sFer8/freETarget-3D-Printed-Housing/Images/Image 1.png

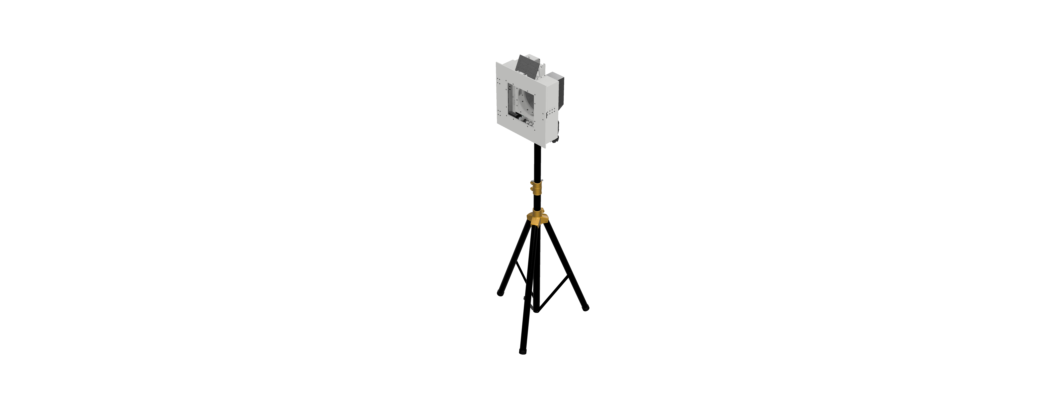
Images/Image 1.png
