sFer8/freETarget-3D-Printed-Housing/Images/Image 2.png

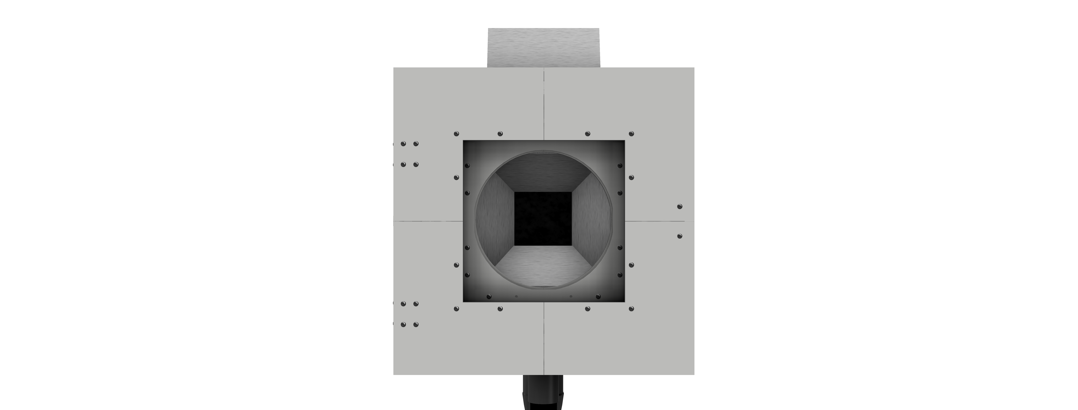
Images/Image 2.png
