sFer8/freETarget-3D-Printed-Housing/Images/Image 5.png

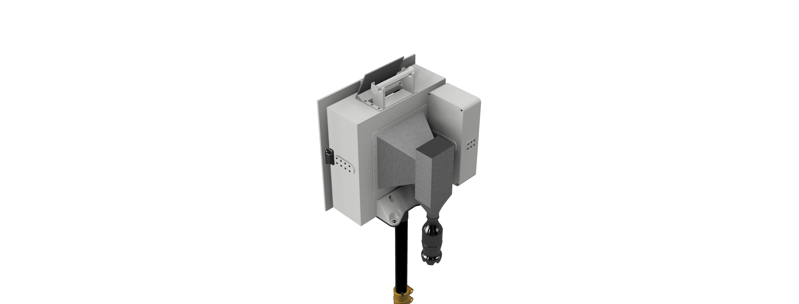
Images/Image 5.png
