sFer8/freETarget-3D-Printed-Housing/Images/Images of Physical Target/IMG_8709.jpg

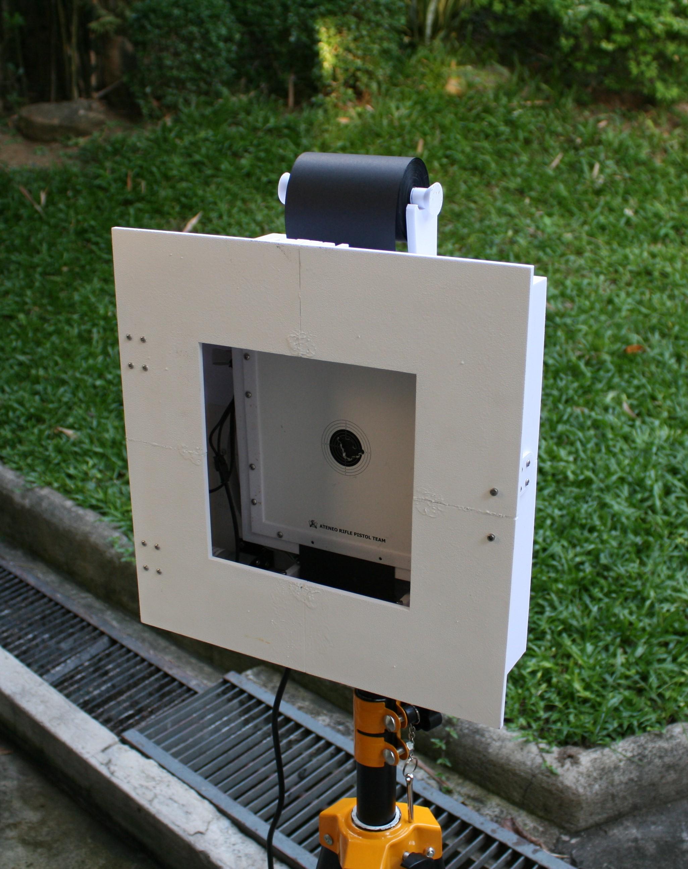
Images/Images of Physical Target/IMG_8709.jpg
