sFer8/freETarget-3D-Printed-Housing/Images/Images of Physical Target/IMG_8710.jpg

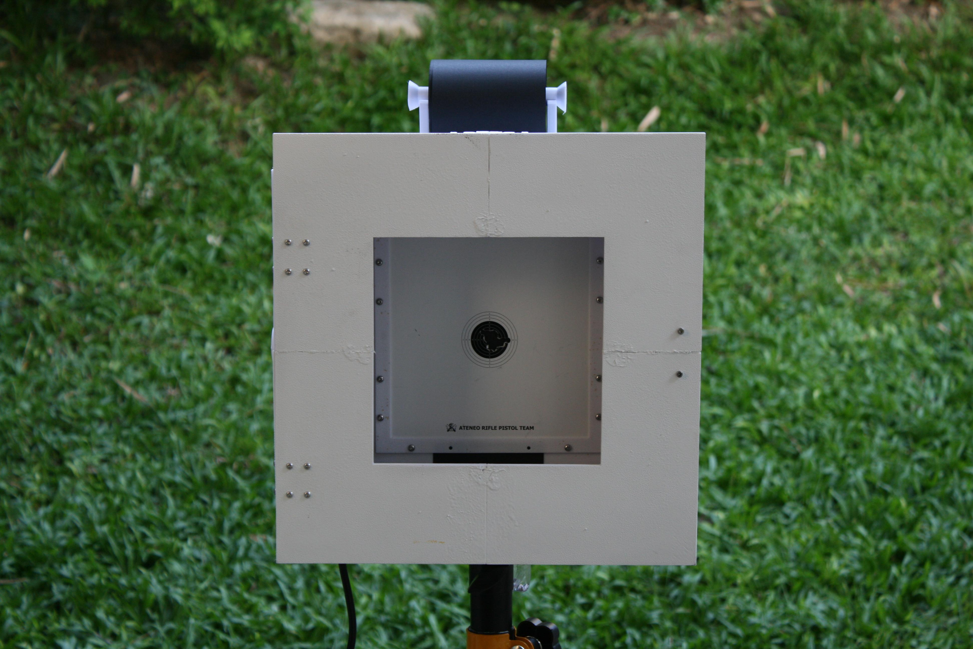
Images/Images of Physical Target/IMG_8710.jpg
