sFer8/freETarget-3D-Printed-Housing/OBJ/Target Holder/Default (17x17cm target)/(3mm Steel )Metal Plate.obj

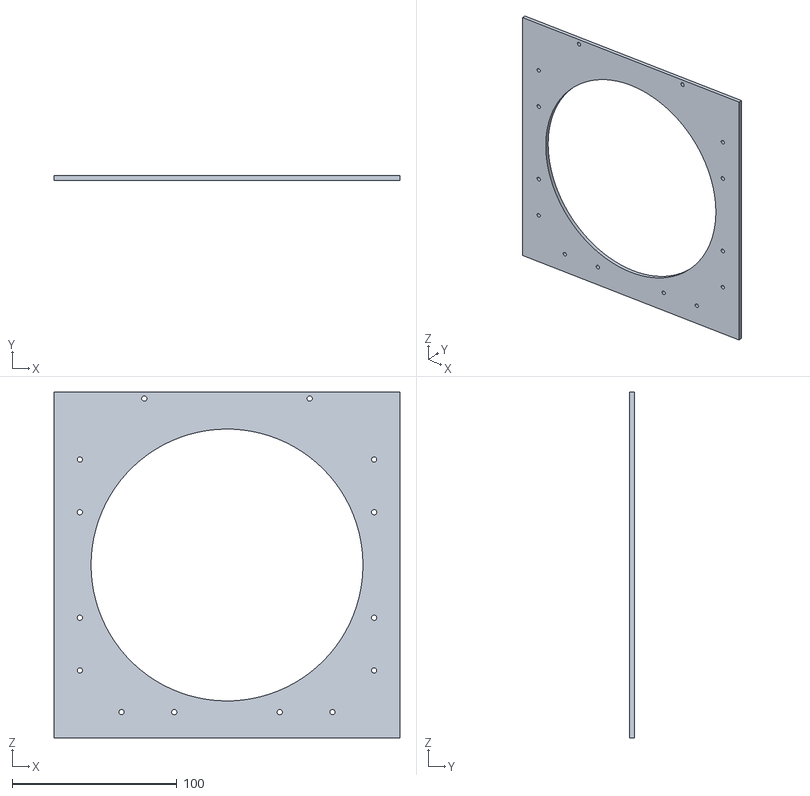
[picture p37: CAD file, 2025-11-06]
OBJ/Target Holder/Default (17x17cm target)/(3mm Steel )Metal Plate.obj
210.0 x 3.00 x 210.0
