sFer8/freETarget-3D-Printed-Housing/OBJ/Target Holder/Witness paper Guide.obj

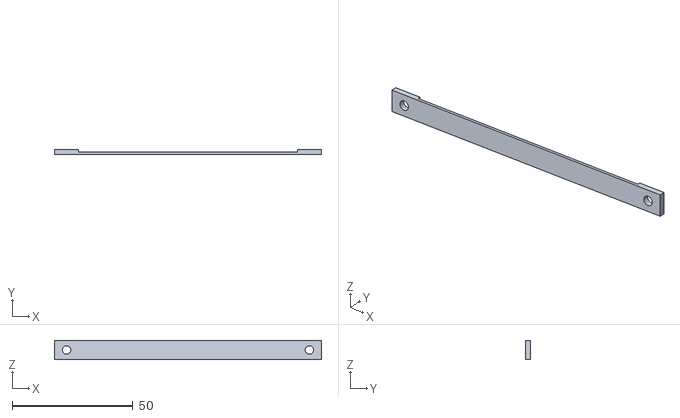
[picture p38: CAD file, 2025-11-06]
OBJ/Target Holder/Witness paper Guide.obj
110.4 x 2.00 x 8.00
