sFer8/freETarget-3D-Printed-Housing/OBJ/Witness Paper Holder/Witness Paper Holder.obj

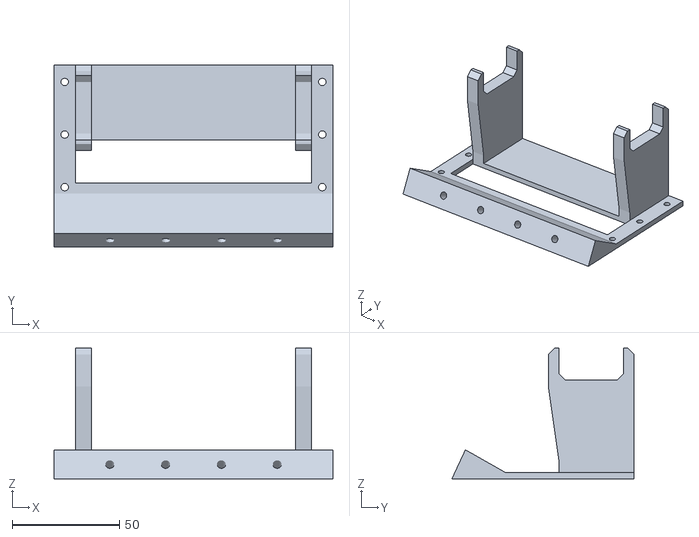
[picture p39: CAD file, 2025-11-06]
OBJ/Witness Paper Holder/Witness Paper Holder.obj
130.0 x 85.0 x 61.0
