sFer8/freETarget-3D-Printed-Housing/DWG/Housing Plate.dxf

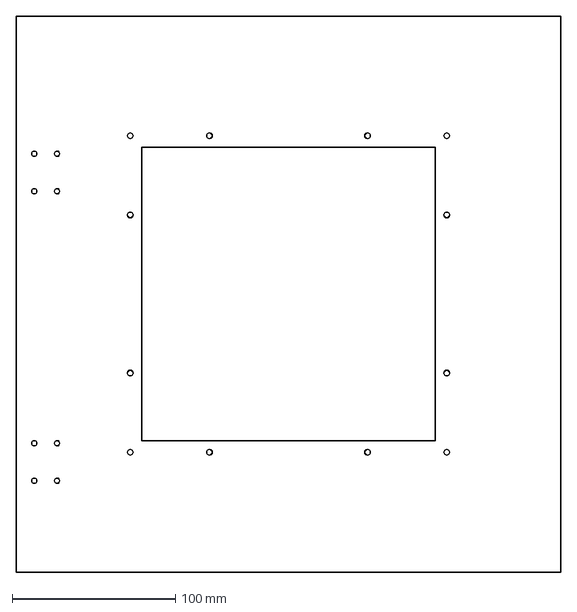
[picture p40: CAD file, 2025-06-11]
DWG/Housing Plate.dxf
334.0 x 341.0 mm
