sFer8/freETarget-3D-Printed-Housing/DXF/SUIS Style Pellet trap/Right.dxf

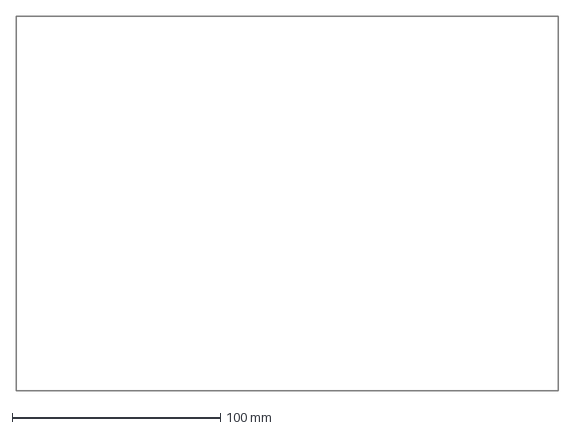
[picture p41: CAD file, 2025-11-06]
DXF/SUIS Style Pellet trap/Right.dxf
260.3 x 180.0 mm
