sFer8/freETarget-3D-Printed-Housing/DXF/SUIS Target Holder Metal Plate.dxf

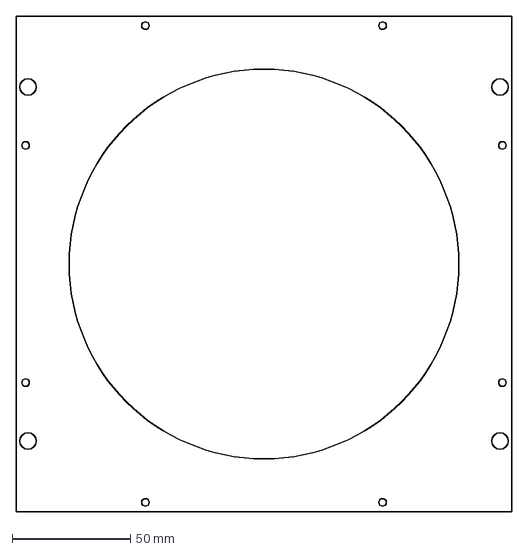
[picture p42: CAD file, 2025-11-06]
DXF/SUIS Target Holder Metal Plate.dxf
210.0 x 210.0 mm
