sFer8/freETarget-3D-Printed-Housing/OBJ/(Steel plates) SUIS Style Pellet trap/(2mm Steel) Bottom.obj

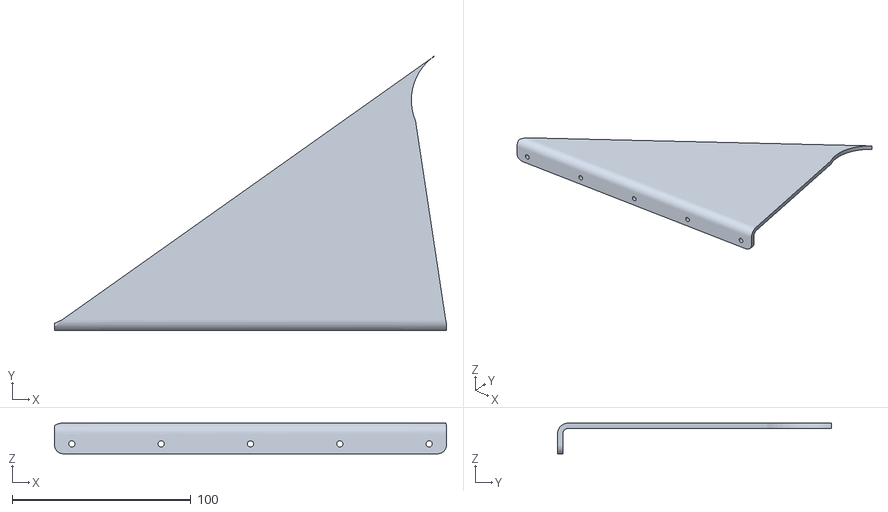
[picture p43: CAD file, 2025-11-06]
OBJ/(Steel plates) SUIS Style Pellet trap/(2mm Steel) Bottom.obj
219.4 x 153.4 x 17.2
