sFer8/freETarget-3D-Printed-Housing/OBJ/Electronics Box/Box/Electronics Box Top.obj

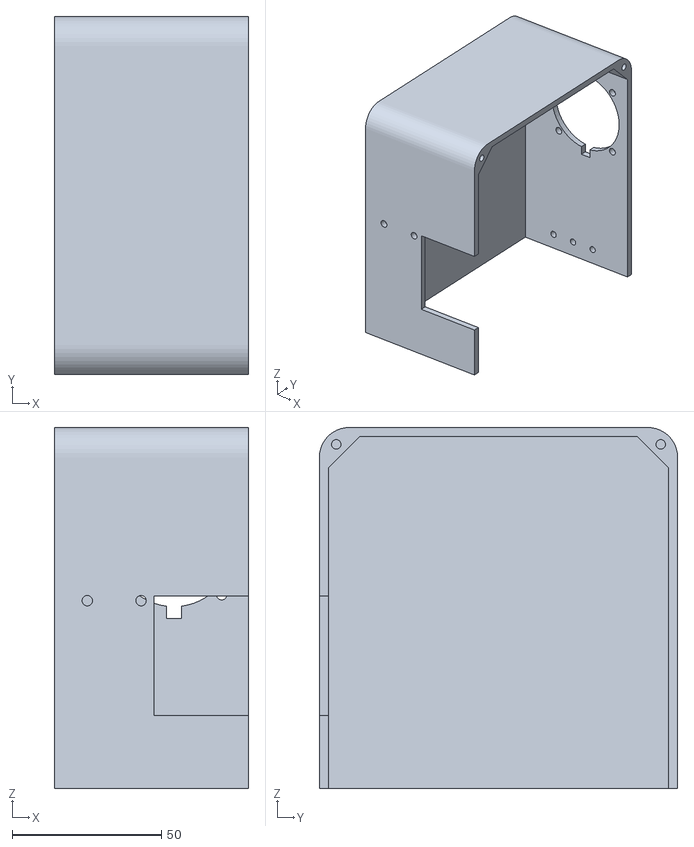
[picture p44: CAD file, 2025-11-06]
OBJ/Electronics Box/Box/Electronics Box Top.obj
65.0 x 120.0 x 120.9
