sFer8/freETarget-3D-Printed-Housing/OBJ/Housing/Face/Top Right.obj

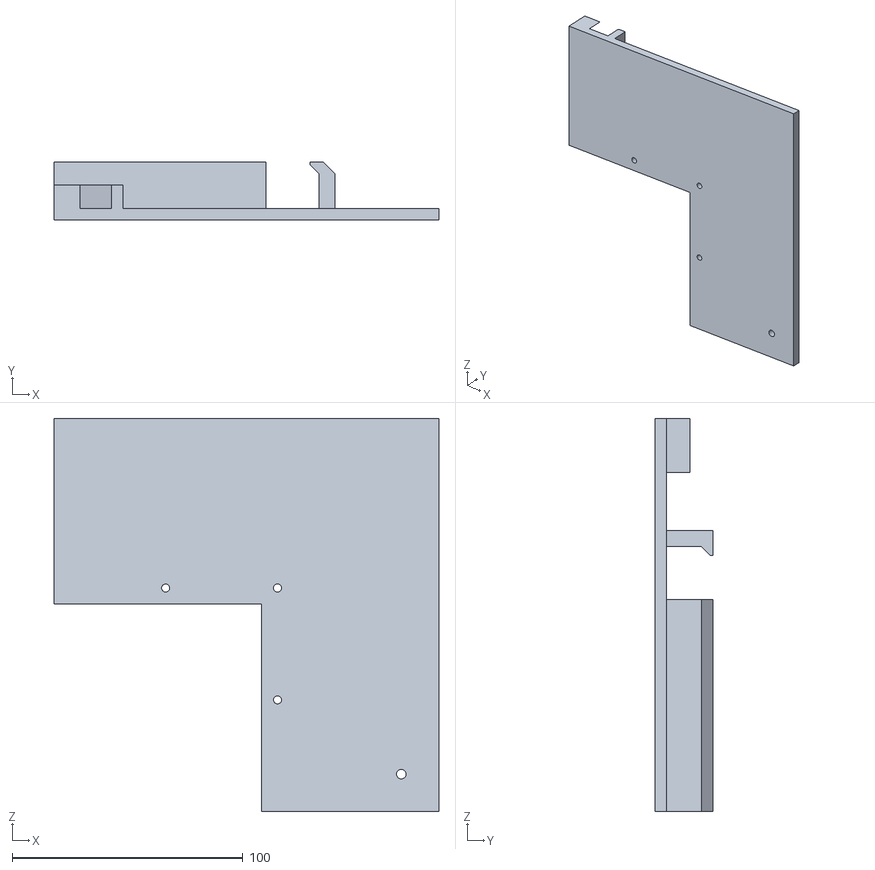
[picture p45: CAD file, 2025-11-06]
OBJ/Housing/Face/Top Right.obj
166.9 x 25.0 x 170.4
