sFer8/freETarget-3D-Printed-Housing/OBJ/Joining Plates/Dovetail wedge Left.obj

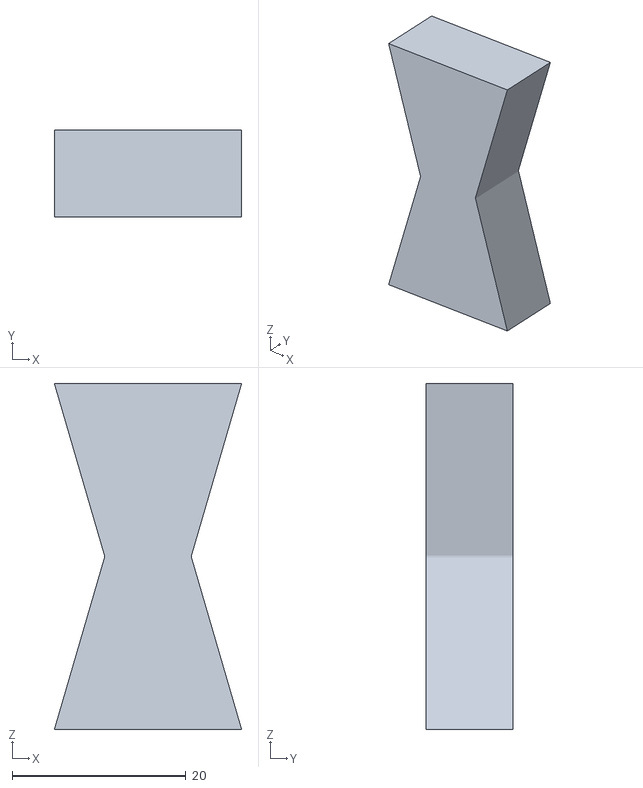
[picture p46: CAD file, 2025-11-06]
OBJ/Joining Plates/Dovetail wedge Left.obj
21.6 x 10.0 x 39.8
