sFer8/freETarget-3D-Printed-Housing/OBJ/Merged/Face Plate.obj

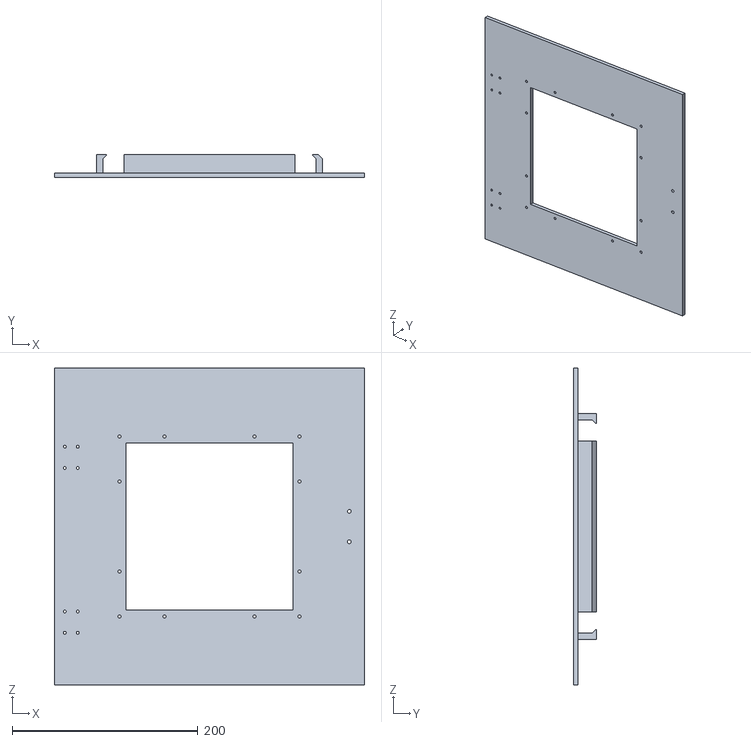
[picture p47: CAD file, 2025-01-14]
OBJ/Merged/Face Plate.obj
334.0 x 25.0 x 341.0
