sFer8/freETarget-3D-Printed-Housing/OBJ/Target Holder/7 Inch wide target/Metal Plate for 7in Target.dxf

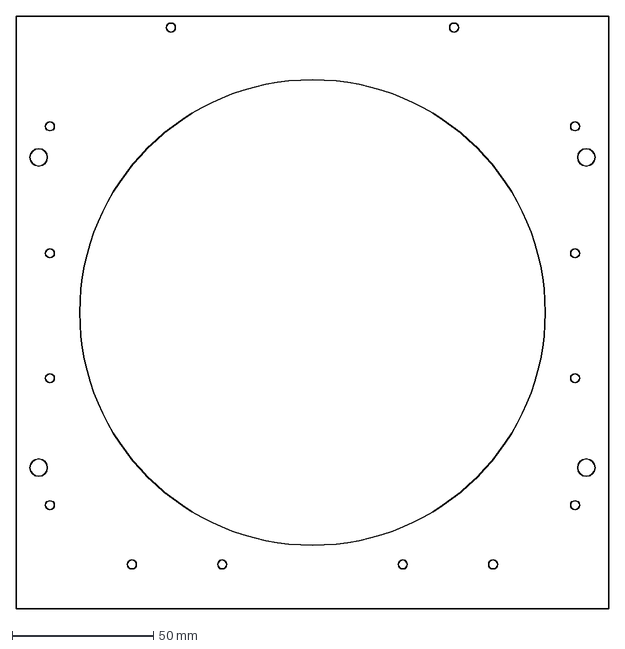
[picture p48: CAD file, 2025-11-23]
OBJ/Target Holder/7 Inch wide target/Metal Plate for 7in Target.dxf
210.0 x 210.0 mm
