sFer8/freETarget-3D-Printed-Housing/OBJ/Target Holder/Default/Targe Holder.obj

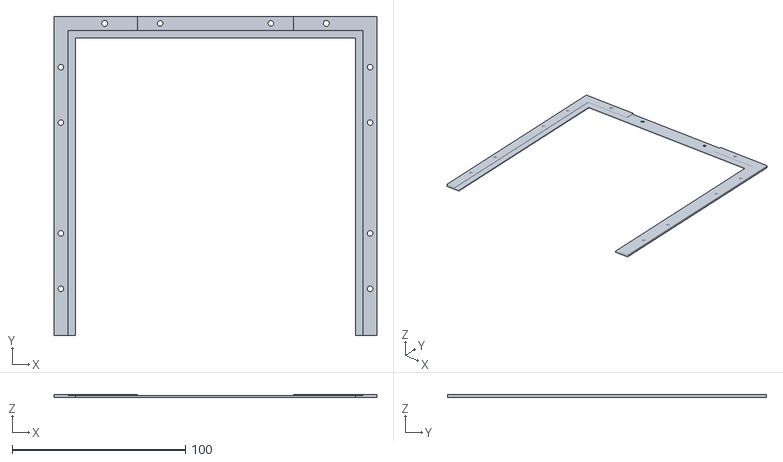
[picture p49: CAD file, 2025-01-06]
OBJ/Target Holder/Default/Targe Holder.obj
186.6 x 184.3 x 2.00
