sFer8/freETarget-3D-Printed-Housing/OBJ/Target Holder/SUIS Target/SUIS Knob 1.obj

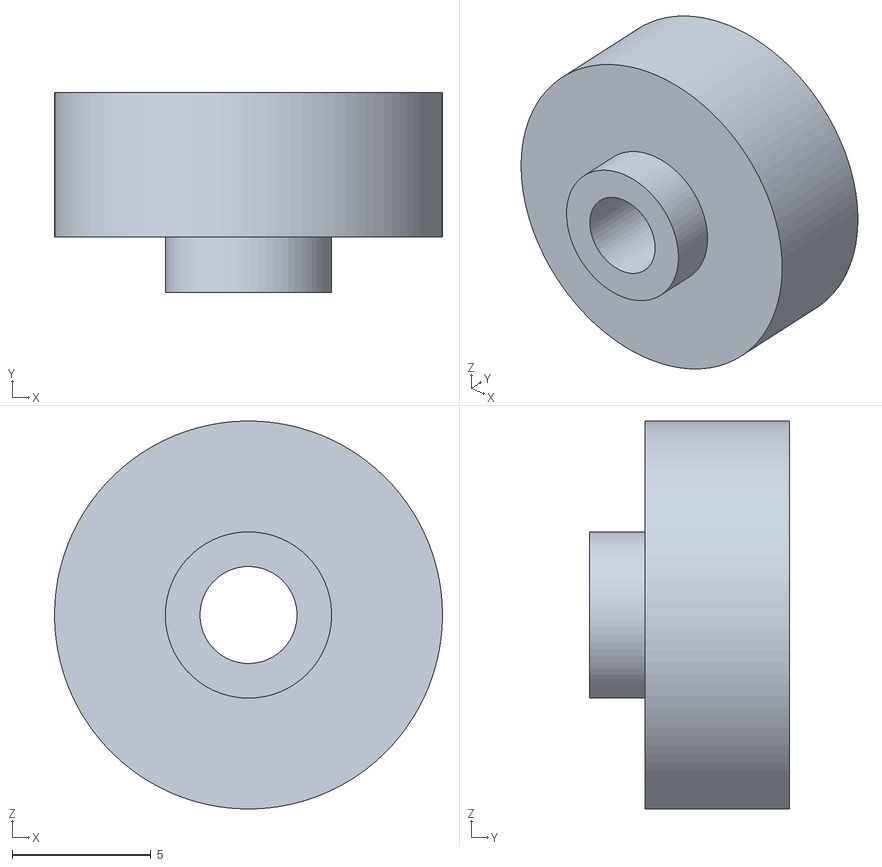
[picture p50: CAD file, 2025-11-06]
OBJ/Target Holder/SUIS Target/SUIS Knob 1.obj
14.0 x 7.20 x 14.0
