sFer8/freETarget-3D-Printed-Housing/OBJ/Witness Paper Holder/(3mm Steel) Steel Pellet Deflector.obj

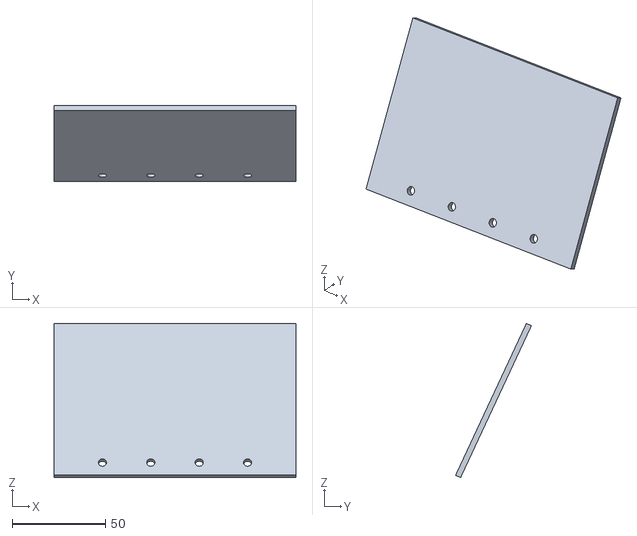
[picture p51: CAD file, 2025-11-06]
OBJ/Witness Paper Holder/(3mm Steel) Steel Pellet Deflector.obj
130.0 x 40.8 x 82.8
