sFer8/freETarget-3D-Printed-Housing/DWG/SIUS metal plate.dxf

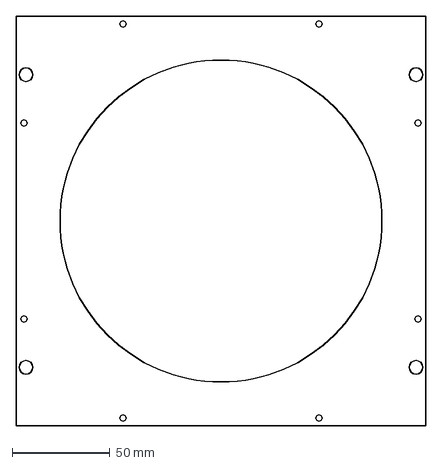
[picture p52: CAD file, 2025-06-11]
DWG/SIUS metal plate.dxf
210.0 x 210.0 mm
