sFer8/freETarget-3D-Printed-Housing/DXF/Housing Metal Plate.dxf

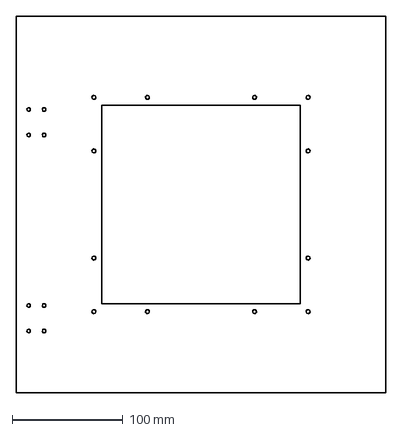
[picture p53: CAD file, 2025-11-06]
DXF/Housing Metal Plate.dxf
334.0 x 341.0 mm
