sFer8/freETarget-3D-Printed-Housing/DXF/SUIS Style Pellet trap/Left.dxf

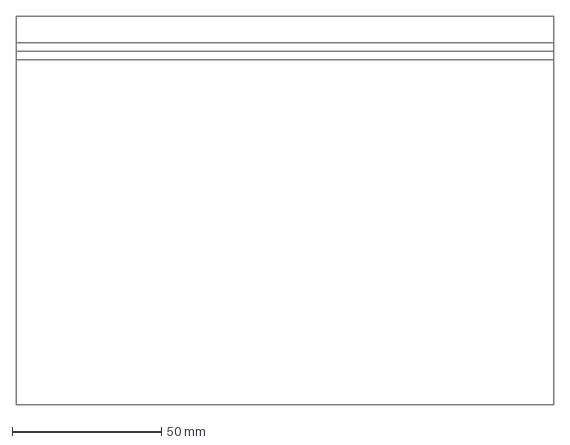
[picture p54: CAD file, 2025-11-06]
DXF/SUIS Style Pellet trap/Left.dxf
180.0 x 130.1 mm
