sFer8/freETarget-3D-Printed-Housing/OBJ/(Steel plates) SUIS Style Pellet trap/(2mm Steel) Left.obj

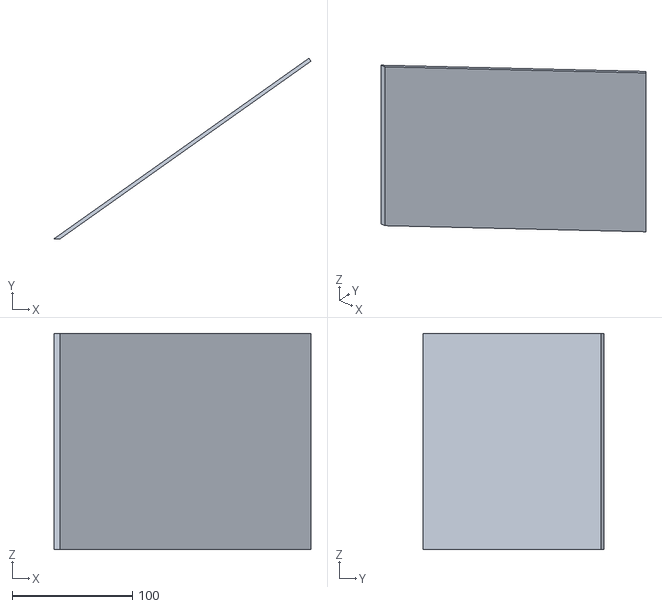
[picture p55: CAD file, 2025-11-06]
OBJ/(Steel plates) SUIS Style Pellet trap/(2mm Steel) Left.obj
214.1 x 150.4 x 180.0
