sFer8/freETarget-3D-Printed-Housing/OBJ/Joining Plates/Electronics Cover Joining Plate.obj

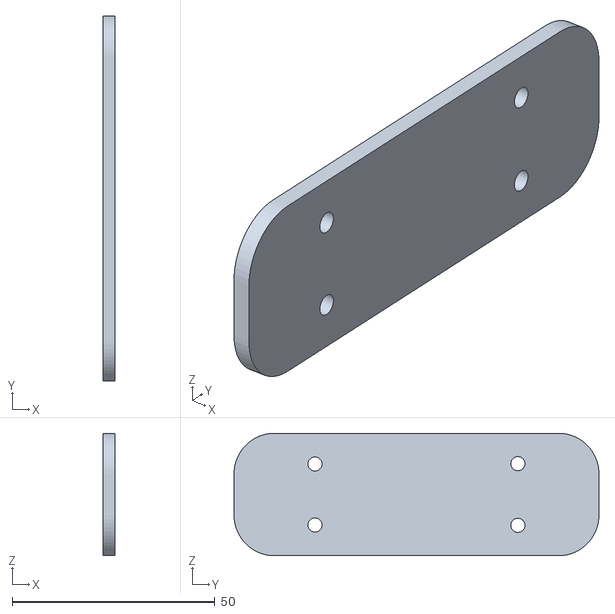
[picture p57: CAD file, 2025-11-06]
OBJ/Joining Plates/Electronics Cover Joining Plate.obj
3.00 x 90.0 x 30.2
