sFer8/freETarget-3D-Printed-Housing/OBJ/Merged/Electronics Box Bottom.obj

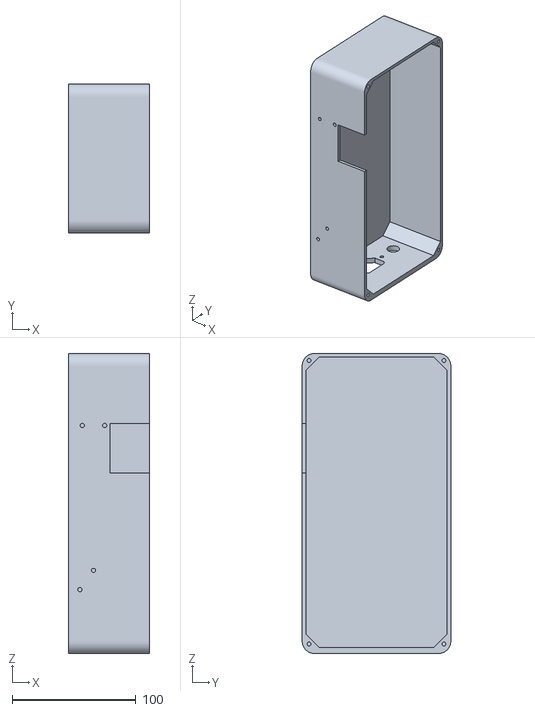
[picture p58: CAD file, 2025-01-14]
OBJ/Merged/Electronics Box Bottom.obj
65.0 x 120.0 x 242.0
