sFer8/freETarget-3D-Printed-Housing/OBJ/Target Holder/7 Inch wide target/Targe Holder 7 in Target.obj

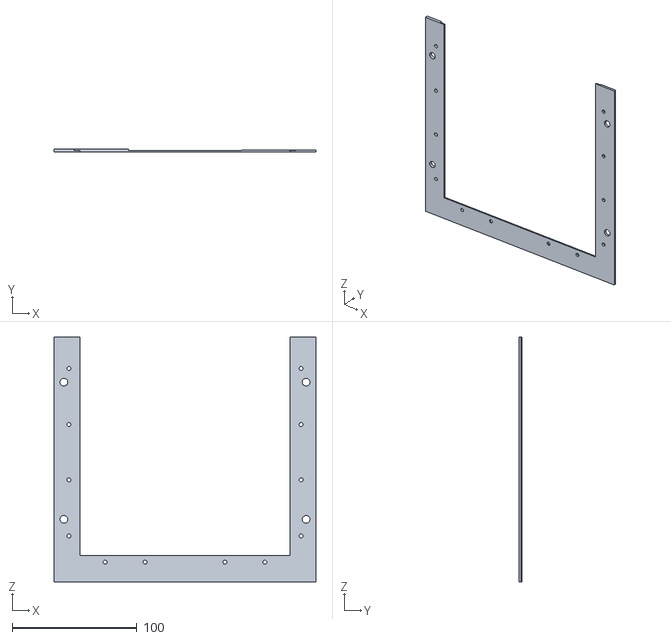
[picture p59: CAD file, 2025-11-23]
OBJ/Target Holder/7 Inch wide target/Targe Holder 7 in Target.obj
210.0 x 2.80 x 196.0
