sFer8/freETarget-3D-Printed-Housing/OBJ/Target Holder/SUIS Target/Target Plate (1).obj

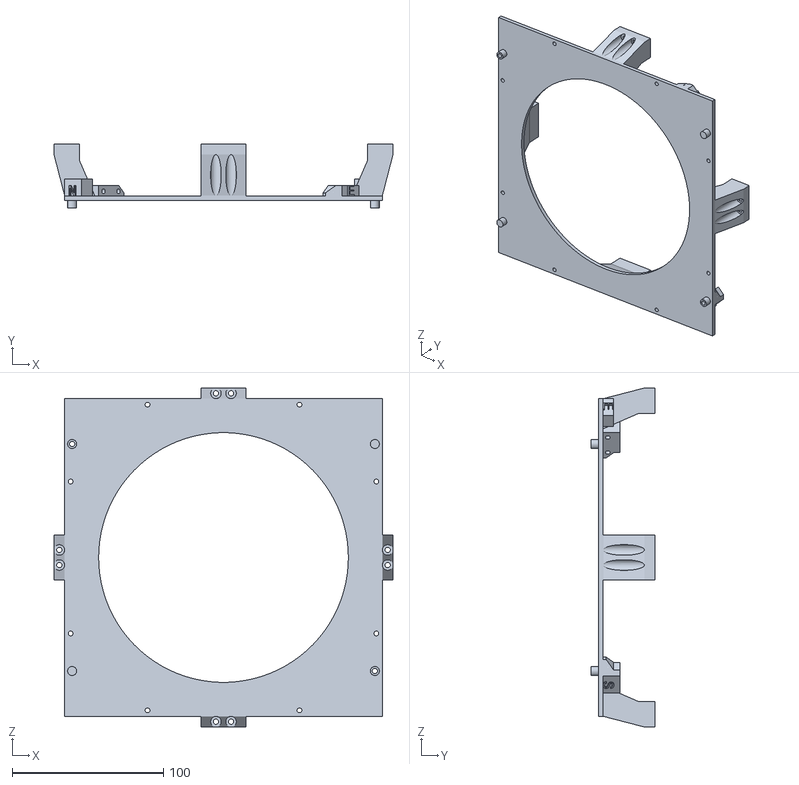
[picture p60: CAD file, 2025-11-06]
OBJ/Target Holder/SUIS Target/Target Plate (1).obj
224.0 x 42.2 x 224.0
