sFer8/freETarget-3D-Printed-Housing/OBJ/Witness Paper Holder/Witness Paper Dowel.obj

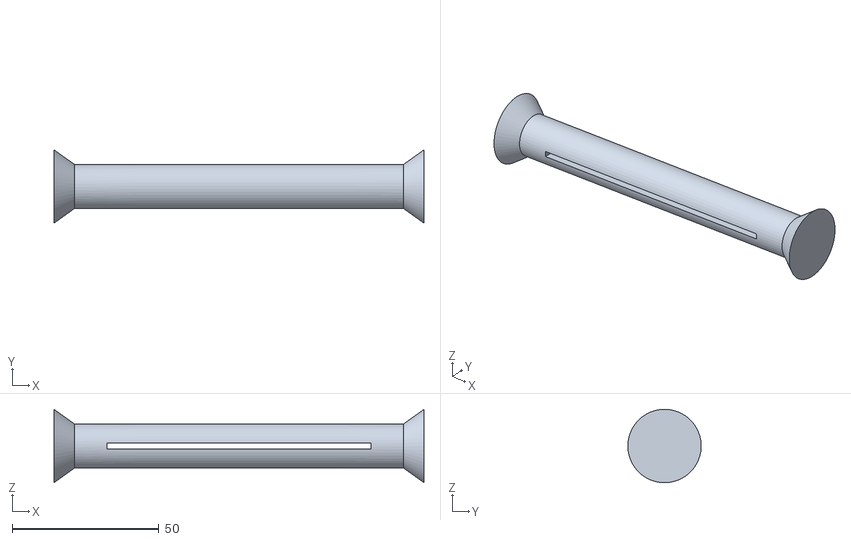
[picture p61: CAD file, 2025-01-06]
OBJ/Witness Paper Holder/Witness Paper Dowel.obj
126.0 x 25.0 x 25.0
