sFer8/freETarget-3D-Printed-Housing/DXF/SUIS Style Pellet trap/Top.dxf

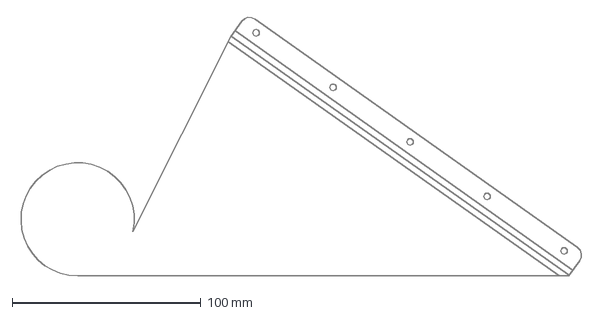
[picture p62: CAD file, 2025-11-06]
DXF/SUIS Style Pellet trap/Top.dxf
300.2 x 137.8 mm
