sFer8/freETarget-3D-Printed-Housing/DXF/Witness Paper Deflector.dxf

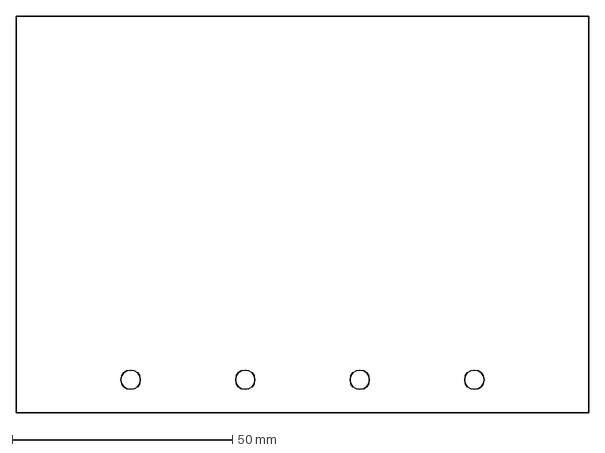
[picture p63: CAD file, 2025-06-11]
DXF/Witness Paper Deflector.dxf
130.0 x 90.0 mm
