sFer8/freETarget-3D-Printed-Housing/OBJ/(Steel plates) SUIS Style Pellet trap/(3mm Steel) Right.obj

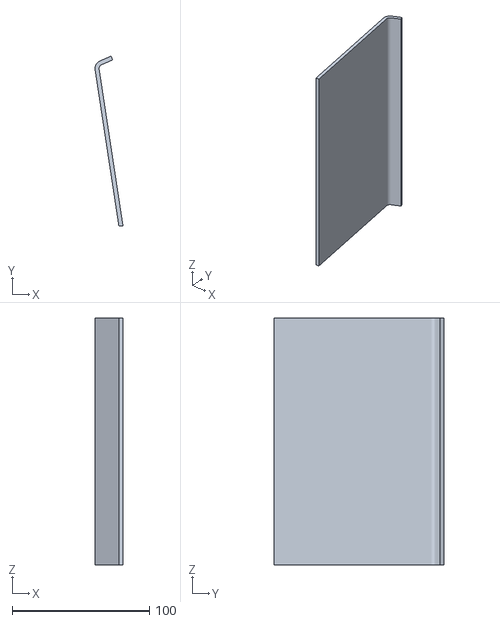
[picture p64: CAD file, 2025-11-06]
OBJ/(Steel plates) SUIS Style Pellet trap/(3mm Steel) Right.obj
20.4 x 123.7 x 180.0
