sFer8/freETarget-3D-Printed-Housing/OBJ/Housing/Face/Bottom Right.obj

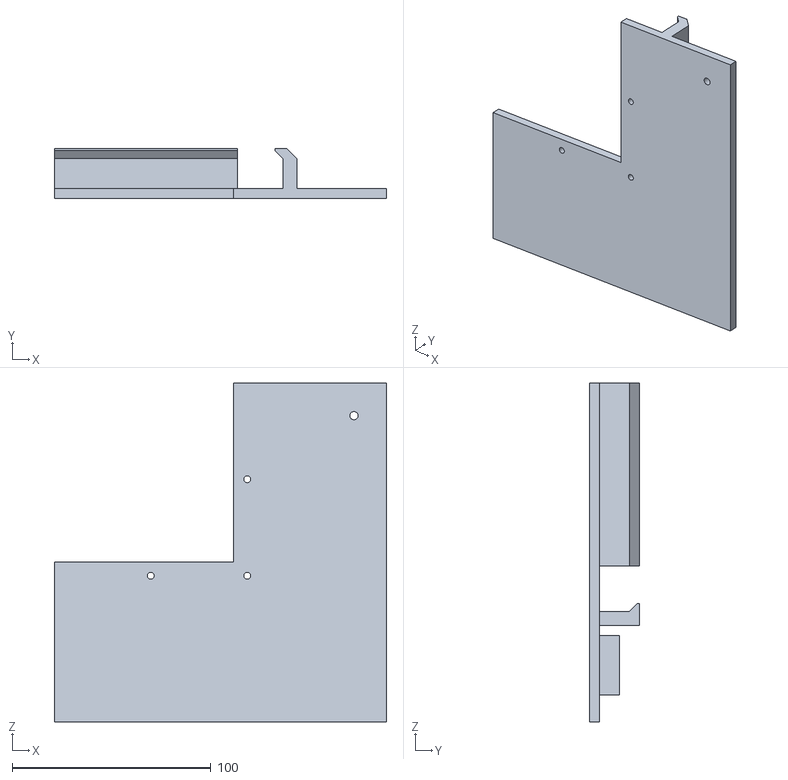
[picture p65: CAD file, 2025-11-06]
OBJ/Housing/Face/Bottom Right.obj
166.9 x 25.0 x 170.4
