sFer8/freETarget-3D-Printed-Housing/OBJ/Joining Plates/Dovetail wedge Top.obj

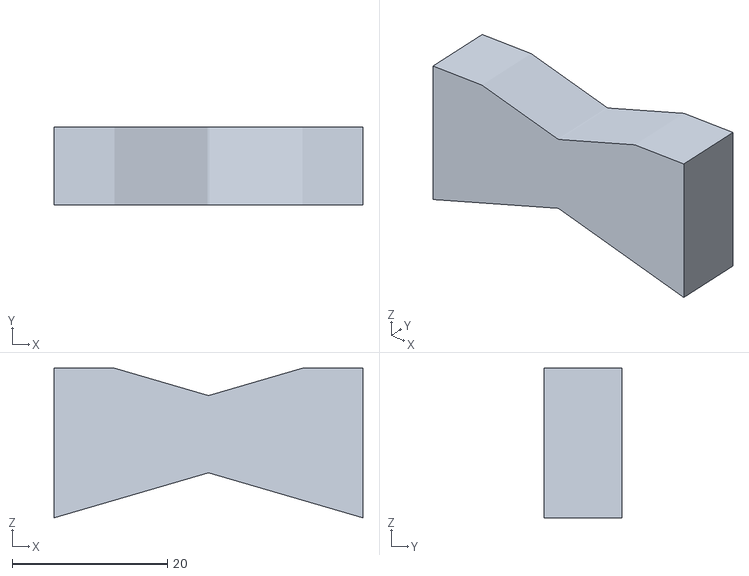
[picture p66: CAD file, 2025-11-06]
OBJ/Joining Plates/Dovetail wedge Top.obj
39.8 x 10.0 x 19.3
