sFer8/freETarget-3D-Printed-Housing/OBJ/Merged/Electronics Cover Bottom.obj

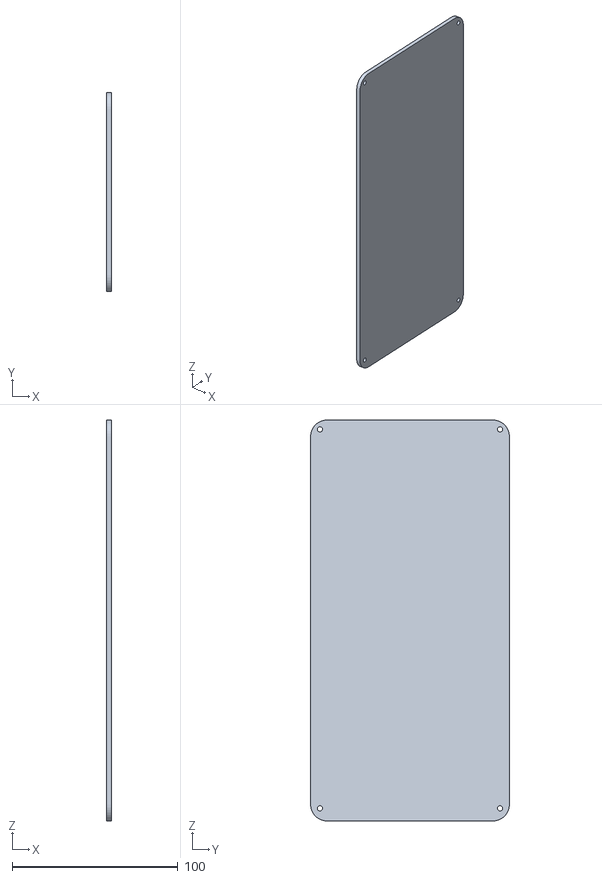
[picture p67: CAD file, 2025-01-14]
OBJ/Merged/Electronics Cover Bottom.obj
3.00 x 120.0 x 242.0
