sFer8/freETarget-3D-Printed-Housing/OBJ/(Steel plates) SUIS Style Pellet trap/(2mm Steel) Top.obj

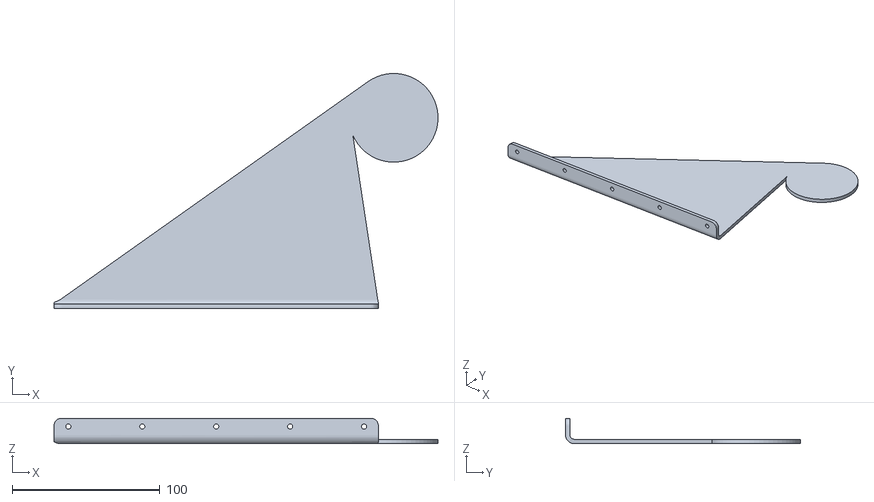
[picture p68: CAD file, 2025-11-06]
OBJ/(Steel plates) SUIS Style Pellet trap/(2mm Steel) Top.obj
259.7 x 158.9 x 17.2
