sFer8/freETarget-3D-Printed-Housing/OBJ/Housing/Face with steel Plate/(3mm Steel) Steel Housing plate.obj

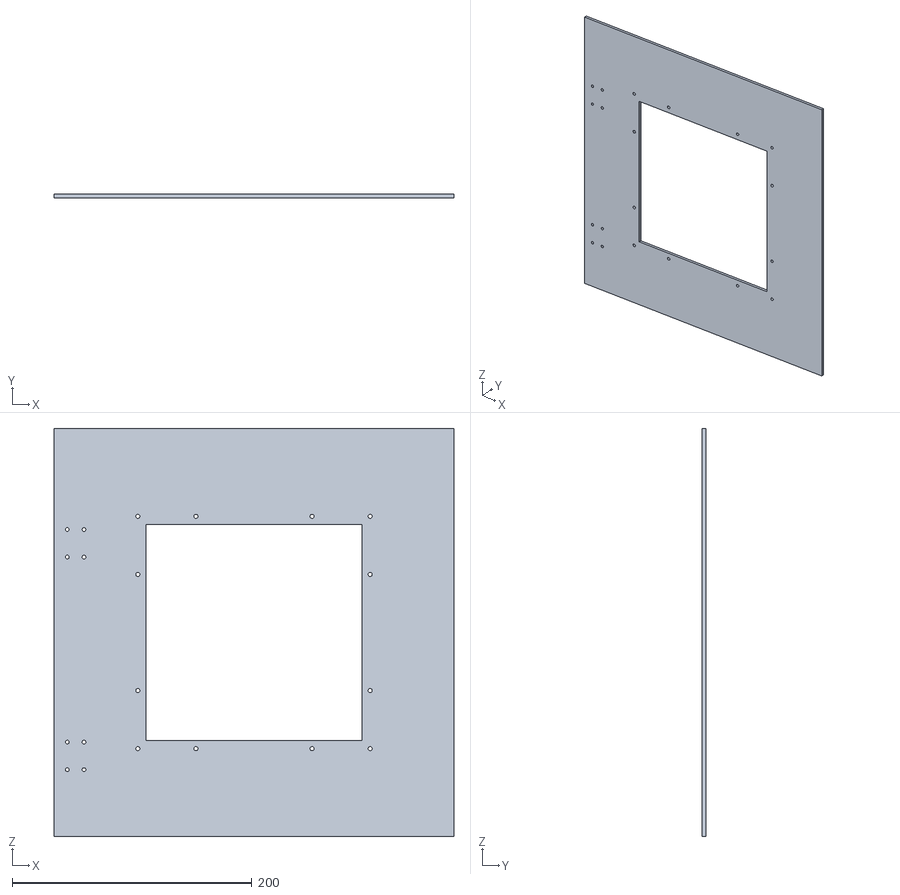
[picture p69: CAD file, 2025-11-06]
OBJ/Housing/Face with steel Plate/(3mm Steel) Steel Housing plate.obj
334.0 x 3.00 x 341.0
