sFer8/freETarget-3D-Printed-Housing/OBJ/Housing/Face/Joining frame.obj

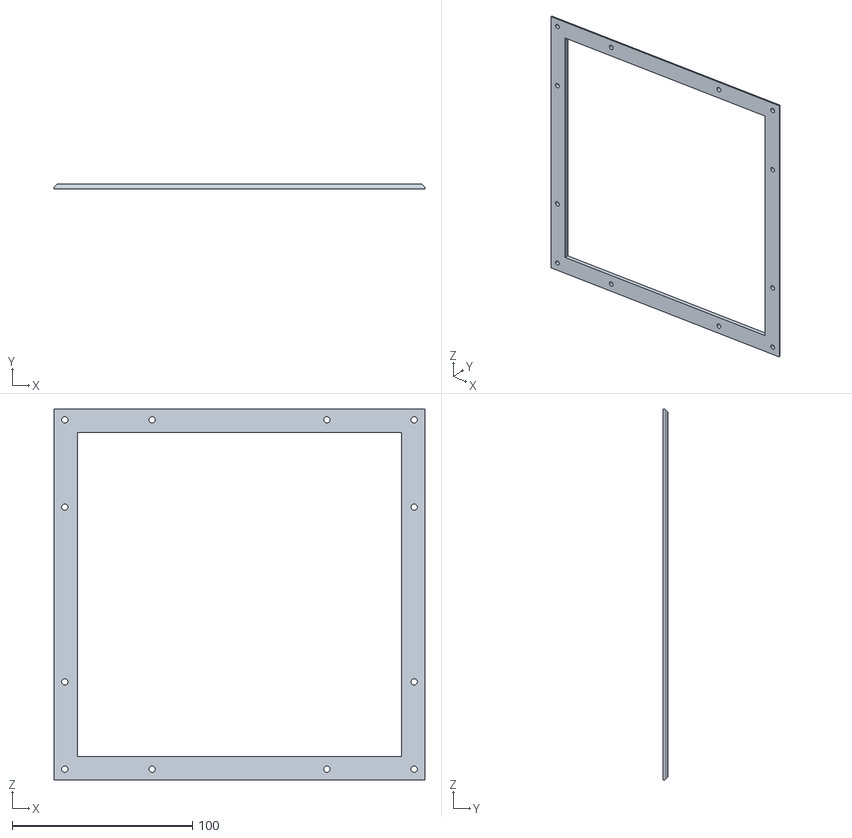
[picture p70: CAD file, 2025-11-06]
OBJ/Housing/Face/Joining frame.obj
206.0 x 3.00 x 206.0
