sFer8/freETarget-3D-Printed-Housing/OBJ/Housing/Main Housing/Bottom Left.obj

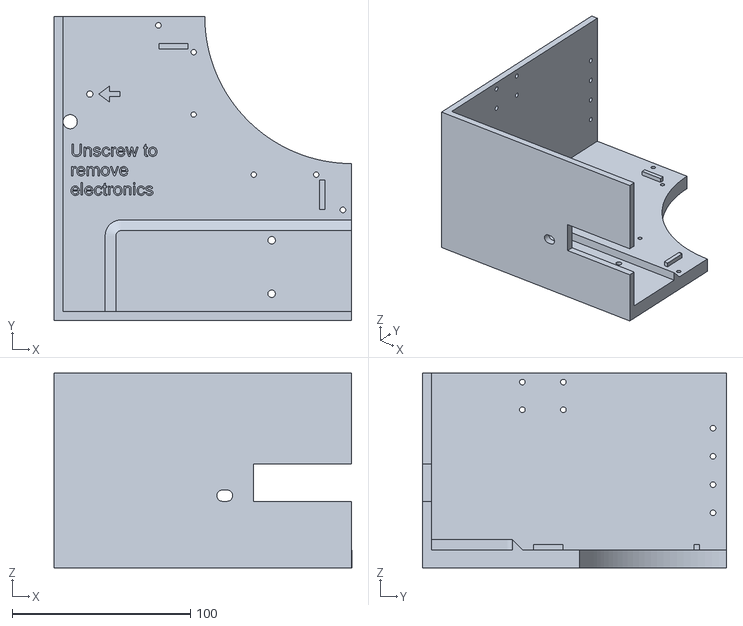
[picture p71: CAD file, 2025-01-06]
OBJ/Housing/Main Housing/Bottom Left.obj
167.0 x 170.5 x 109.2
