sFer8/freETarget-3D-Printed-Housing/OBJ/Joining Plates/Right Joining Plate.obj

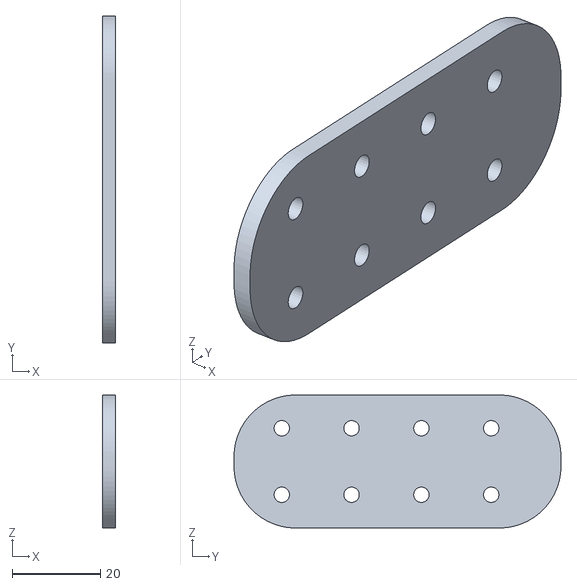
[picture p72: CAD file, 2025-11-06]
OBJ/Joining Plates/Right Joining Plate.obj
3.00 x 74.2 x 30.2
