sFer8/freETarget-3D-Printed-Housing/OBJ/Target Holder/SUIS Target/SUIS Target Plate.obj

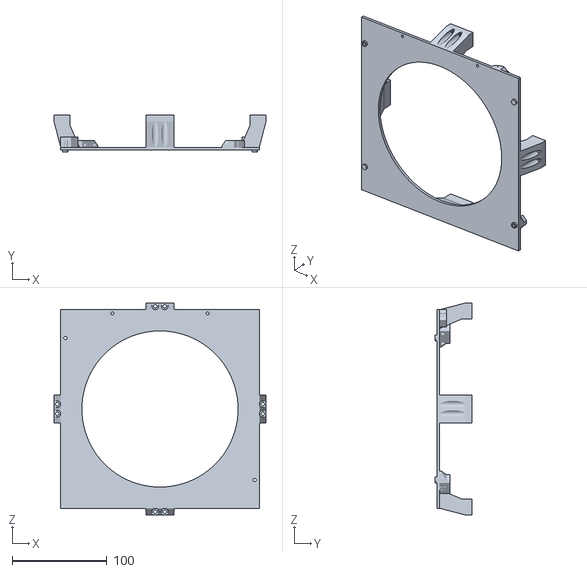
[picture p73: CAD file, 2025-01-08]
OBJ/Target Holder/SUIS Target/SUIS Target Plate.obj
224.0 x 39.2 x 224.0
