sFer8/freETarget-3D-Printed-Housing/OBJ/(Steel plates) SUIS Style Pellet trap/Bottle Adapter.obj

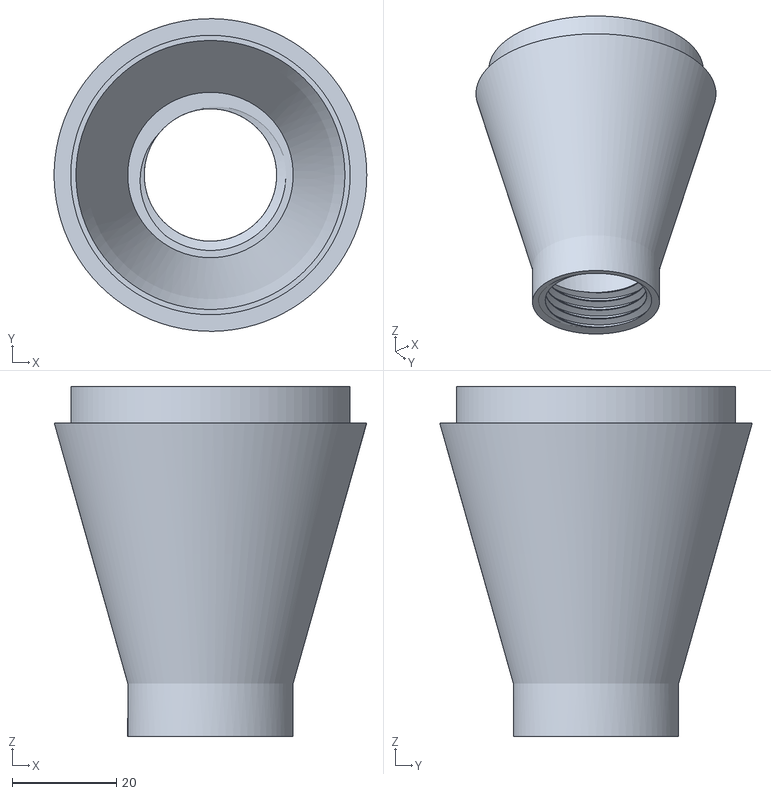
[picture p74: CAD file, 2025-11-06]
OBJ/(Steel plates) SUIS Style Pellet trap/Bottle Adapter.obj
60.0 x 60.0 x 67.2
