sFer8/freETarget-3D-Printed-Housing/OBJ/Housing/Main Housing/Top Left.obj

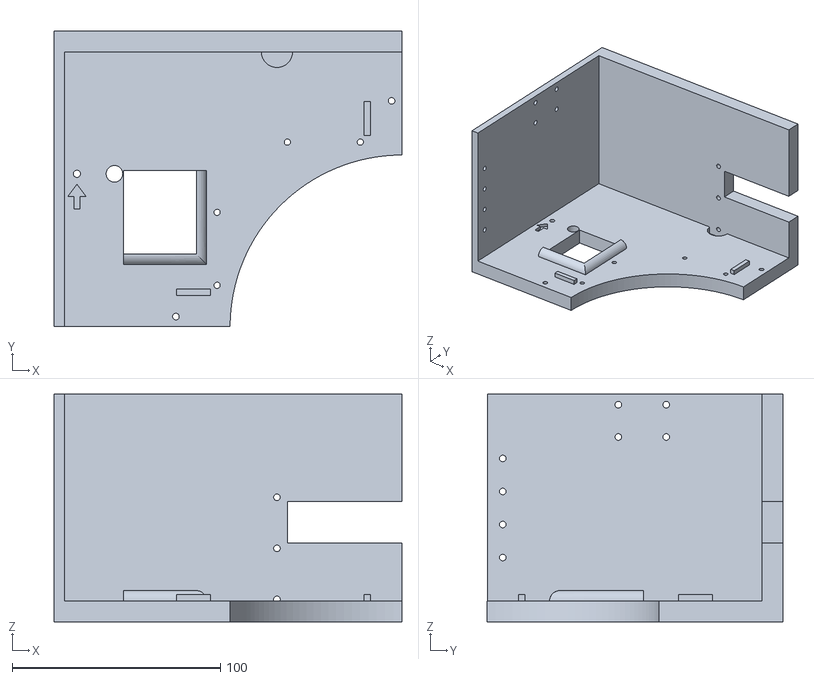
[picture p75: CAD file, 2025-01-06]
OBJ/Housing/Main Housing/Top Left.obj
167.0 x 142.0 x 109.2
