sFer8/freETarget-3D-Printed-Housing/OBJ/Joining Plates/Electronics Joining Plate.obj

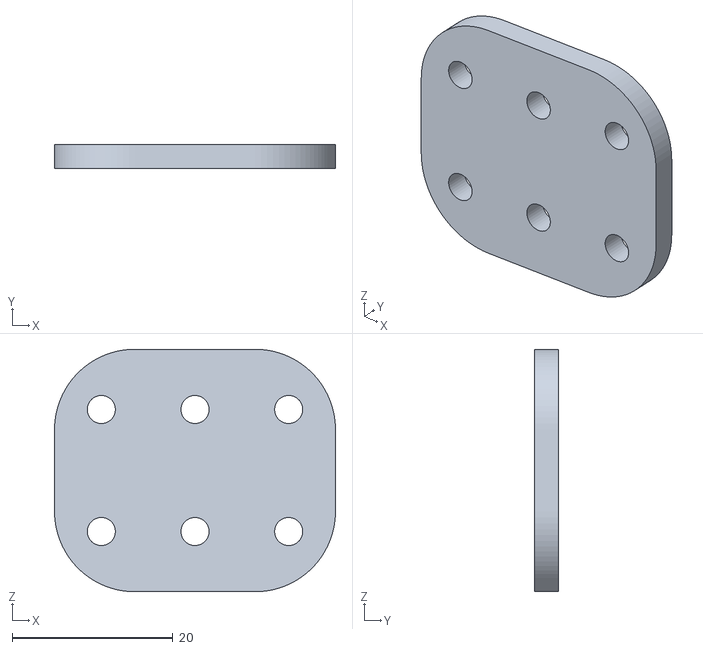
[picture p76: CAD file, 2025-11-06]
OBJ/Joining Plates/Electronics Joining Plate.obj
35.0 x 3.00 x 30.2
