sFer8/freETarget-3D-Printed-Housing/OBJ/Housing/Main Housing/Bottom Right.obj

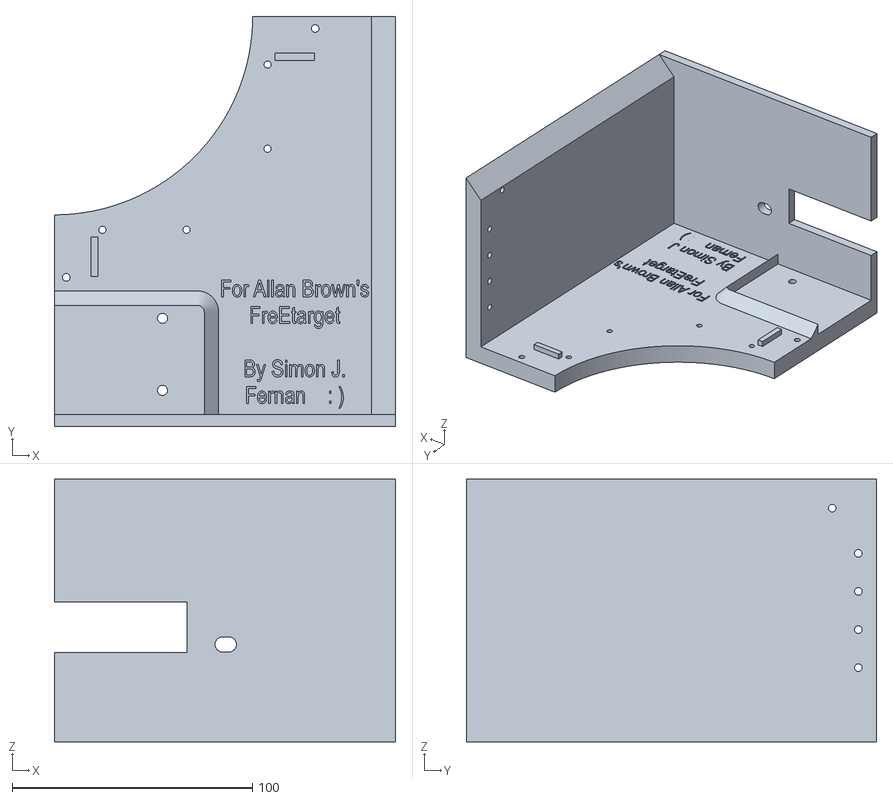
[picture p77: CAD file, 2025-01-06]
OBJ/Housing/Main Housing/Bottom Right.obj
142.0 x 170.5 x 109.2
