sFer8/freETarget-3D-Printed-Housing/OBJ/Housing/Main Housing/Top Right.obj

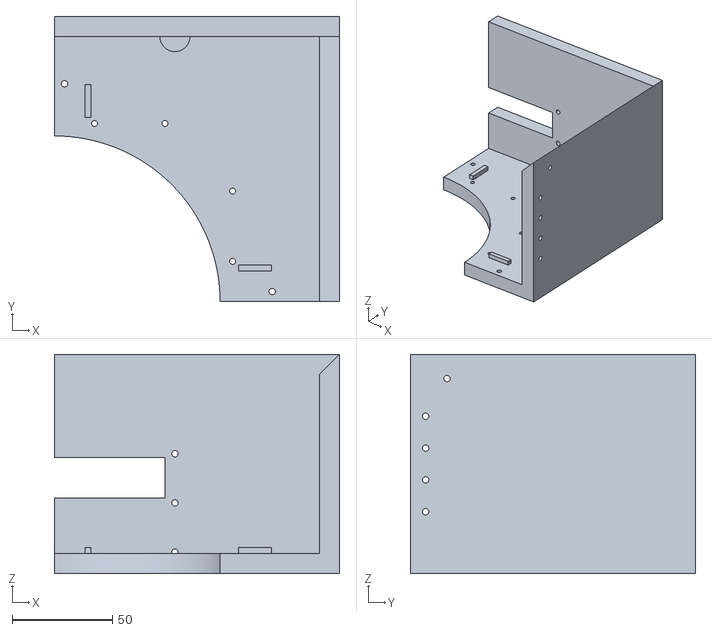
[picture p78: CAD file, 2025-01-06]
OBJ/Housing/Main Housing/Top Right.obj
142.0 x 142.0 x 109.2
